rupin-r/MPU6050_MotionTracking_ProofofConcept/imu_fixed_inputs_no_softmax/cnn.c

/*******************************************************************************
* Copyright (C) 2019-2024 Maxim Integrated Products, Inc., All rights Reserved.
*
* This software is protected by copyright laws of the United States and
* of foreign countries. This material may also be protected by patent laws
* and technology transfer regulations of the United States and of foreign
* countries. This software is furnished under a license agreement and/or a
* nondisclosure agreement and may only be used or reproduced in accordance
* with the terms of those agreements. Dissemination of this information to
* any party or parties not specified in the license agreement and/or
* nondisclosure agreement is expressly prohibited.
*
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
* Except as contained in this notice, the name of Maxim Integrated
* Products, Inc. shall not be used except as stated in the Maxim Integrated
* Products, Inc. Branding Policy.
*
* The mere transfer of this software does not imply any licenses
* of trade secrets, proprietary technology, copyrights, patents,
* trademarks, maskwork rights, or any other form of intellectual
* property whatsoever. Maxim Integrated Products, Inc. retains all
* ownership rights.
*******************************************************************************/

// imu_fixed_inputs_no_softmax
// This file was @generated by ai8xize.py --verbose --test-dir demos --prefix imu_fixed_inputs_no_softmax --checkpoint-file trained/imu_q8.pth.tar --config-file networks/imu.yaml --device MAX78000 --compact-data

// DO NOT EDIT - regenerate this file instead!

// Configuring 6 layers
// Input data: HWC
// Layer 0: 30x6x6, no pooling, convtranspose2d with kernel size 3x3, stride 2/2, pad 1/1, no activation, 16x12x12 output
// Layer 1: 16x12x12, no pooling, convtranspose2d with kernel size 3x3, stride 2/2, pad 1/1, no activation, 8x24x24 output
// Layer 2: 8x24x24, no pooling, conv2d with kernel size 3x3, stride 1/1, pad 1/1, ReLU, 8x24x24 output
// Layer 3: 8x24x24, max pool 2x2 with stride 2/2, conv2d with kernel size 3x3, stride 1/1, pad 1/1, ReLU, 8x12x12 output
// Layer 4: 8x12x12, max pool 4x4 with stride 4/4, conv2d with kernel size 3x3, stride 1/1, pad 1/1, ReLU, 5x3x3 output
// Layer 5: 5x3x3 flattened to 45x1x1, no pooling, linear, no activation, 5x1x1 output

// Final Scales: {0: 0, 1: 0, 2: 0, 3: 0, 4: 0, 5: 6}

#include <stdlib.h>
#include <stdint.h>
#include <string.h>
#include <stdio.h>
#include "mxc.h"
#include "gcfr_regs.h"
#include "cnn.h"
#include "weights.h"

void CNN_ISR(void)
{
  // Acknowledge interrupt to all quadrants
  *((volatile uint32_t *) 0x50100000) &= ~((1<<12) | 1);
  *((volatile uint32_t *) 0x50500000) &= ~((1<<12) | 1);
  *((volatile uint32_t *) 0x50900000) &= ~((1<<12) | 1);
  *((volatile uint32_t *) 0x50d00000) &= ~((1<<12) | 1);

  CNN_COMPLETE; // Signal that processing is complete
#ifdef CNN_INFERENCE_TIMER
  cnn_time = MXC_TMR_SW_Stop(CNN_INFERENCE_TIMER);
#else
  cnn_time = 1;
#endif
}

int cnn_continue(void)
{
  cnn_time = 0;

  *((volatile uint32_t *) 0x50100000) |= 1; // Re-enable quadrant 0

  return CNN_OK;
}

int cnn_stop(void)
{
  *((volatile uint32_t *) 0x50100000) &= ~1; // Disable quadrant 0

  return CNN_OK;
}

void memcpy32(uint32_t *dst, const uint32_t *src, int n)
{
  while (n-- > 0) {
    *dst++ = *src++;
  }
}

static const uint32_t kernels[] = KERNELS;

int cnn_load_weights(void)
{
  uint32_t len;
  volatile uint32_t *addr;
  const uint32_t *ptr = kernels;

  while ((addr = (volatile uint32_t *) *ptr++) != 0) {
    *((volatile uint8_t *) ((uint32_t) addr | 1)) = 0x01; // Set address
    len = *ptr++;
    while (len-- > 0)
      *addr++ = *ptr++;
  }

  return CNN_OK;
}

static const uint8_t bias_0[] = BIAS_0;
static const uint8_t bias_1[] = BIAS_1;
static const uint8_t bias_2[] = BIAS_2;
static const uint8_t bias_3[] = BIAS_3;

static void memcpy_8to32(uint32_t *dst, const uint8_t *src, int n)
{
  while (n-- > 0) {
    *dst++ = *src++;
  }
}

int cnn_load_bias(void)
{
  memcpy_8to32((uint32_t *) 0x50108000, bias_0, sizeof(uint8_t) * 13);
  memcpy_8to32((uint32_t *) 0x50508000, bias_1, sizeof(uint8_t) * 16);
  memcpy_8to32((uint32_t *) 0x50908000, bias_2, sizeof(uint8_t) * 13);
  memcpy_8to32((uint32_t *) 0x50d08000, bias_3, sizeof(uint8_t) * 8);

  return CNN_OK;
}

int cnn_init(void)
{
  *((volatile uint32_t *) 0x50001000) = 0x00000000; // AON control
  *((volatile uint32_t *) 0x50100000) = 0x00100008; // Stop SM
  *((volatile uint32_t *) 0x50100004) = 0x0000040e; // SRAM control
  *((volatile uint32_t *) 0x50100008) = 0x00000005; // Layer count
  *((volatile uint32_t *) 0x50500000) = 0x00100008; // Stop SM
  *((volatile uint32_t *) 0x50500004) = 0x0000040e; // SRAM control
  *((volatile uint32_t *) 0x50500008) = 0x00000005; // Layer count
  *((volatile uint32_t *) 0x50900000) = 0x00100008; // Stop SM
  *((volatile uint32_t *) 0x50900004) = 0x0000040e; // SRAM control
  *((volatile uint32_t *) 0x50900008) = 0x00000005; // Layer count
  *((volatile uint32_t *) 0x50d00000) = 0x00100008; // Stop SM
  *((volatile uint32_t *) 0x50d00004) = 0x0000040e; // SRAM control
  *((volatile uint32_t *) 0x50d00008) = 0x00000005; // Layer count

  return CNN_OK;
}

int cnn_configure(void)
{
  // Layer 0 quadrant 0
  *((volatile uint32_t *) 0x50100010) = 0x0001000d; // Rows
  *((volatile uint32_t *) 0x50100090) = 0x0001000d; // Columns
  *((volatile uint32_t *) 0x50100310) = 0x00011000; // SRAM write ptr
  *((volatile uint32_t *) 0x50100410) = 0x00002000; // Write ptr mask offs
  *((volatile uint32_t *) 0x50100590) = 0x00002920; // Layer control
  *((volatile uint32_t *) 0x50100a10) = 0x00007800; // Layer control 2
  *((volatile uint32_t *) 0x50100610) = 0x00000078; // Mask offset and count
  *((volatile uint32_t *) 0x50100690) = 0x0000000b; // TRAM ptr max
  *((volatile uint32_t *) 0x50100790) = 0x10028000; // Post processing register
  *((volatile uint32_t *) 0x50100710) = 0xffffffff; // Mask and processor enables

  // Layer 0 quadrant 1
  *((volatile uint32_t *) 0x50500010) = 0x0001000d; // Rows
  *((volatile uint32_t *) 0x50500090) = 0x0001000d; // Columns
  *((volatile uint32_t *) 0x50500310) = 0x00011000; // SRAM write ptr
  *((volatile uint32_t *) 0x50500410) = 0x00002000; // Write ptr mask offs
  *((volatile uint32_t *) 0x50500590) = 0x00000920; // Layer control
  *((volatile uint32_t *) 0x50500a10) = 0x00007800; // Layer control 2
  *((volatile uint32_t *) 0x50500610) = 0x00000078; // Mask offset and count
  *((volatile uint32_t *) 0x50500690) = 0x0000000b; // TRAM ptr max
  *((volatile uint32_t *) 0x50500790) = 0x10029000; // Post processing register
  *((volatile uint32_t *) 0x50500710) = 0x3fff3fff; // Mask and processor enables

  // Layer 0 quadrant 2
  *((volatile uint32_t *) 0x50900010) = 0x0001000d; // Rows
  *((volatile uint32_t *) 0x50900090) = 0x0001000d; // Columns
  *((volatile uint32_t *) 0x50900310) = 0x00011000; // SRAM write ptr
  *((volatile uint32_t *) 0x50900410) = 0x00002000; // Write ptr mask offs
  *((volatile uint32_t *) 0x50900590) = 0x00000920; // Layer control
  *((volatile uint32_t *) 0x50900a10) = 0x00007800; // Layer control 2
  *((volatile uint32_t *) 0x50900610) = 0x00000078; // Mask offset and count
  *((volatile uint32_t *) 0x50900690) = 0x0000000b; // TRAM ptr max
  *((volatile uint32_t *) 0x50900790) = 0x10028000; // Post processing register

  // Layer 0 quadrant 3
  *((volatile uint32_t *) 0x50d00010) = 0x0001000d; // Rows
  *((volatile uint32_t *) 0x50d00090) = 0x0001000d; // Columns
  *((volatile uint32_t *) 0x50d00310) = 0x00011000; // SRAM write ptr
  *((volatile uint32_t *) 0x50d00410) = 0x00002000; // Write ptr mask offs
  *((volatile uint32_t *) 0x50d00590) = 0x00000920; // Layer control
  *((volatile uint32_t *) 0x50d00a10) = 0x00007800; // Layer control 2
  *((volatile uint32_t *) 0x50d00610) = 0x00000078; // Mask offset and count
  *((volatile uint32_t *) 0x50d00690) = 0x0000000b; // TRAM ptr max
  *((volatile uint32_t *) 0x50d00790) = 0x10028000; // Post processing register

  // Layer 1 quadrant 0
  *((volatile uint32_t *) 0x50100014) = 0x00010019; // Rows
  *((volatile uint32_t *) 0x50100094) = 0x00010019; // Columns
  *((volatile uint32_t *) 0x50100314) = 0x0001c000; // SRAM write ptr
  *((volatile uint32_t *) 0x50100414) = 0x00002000; // Write ptr mask offs
  *((volatile uint32_t *) 0x50100514) = 0x00001000; // SRAM read ptr
  *((volatile uint32_t *) 0x50100594) = 0x00004920; // Layer control
  *((volatile uint32_t *) 0x50100a14) = 0x00003800; // Layer control 2
  *((volatile uint32_t *) 0x50100614) = 0x00000038; // Mask offset and count
  *((volatile uint32_t *) 0x50100694) = 0x00000017; // TRAM ptr max
  *((volatile uint32_t *) 0x50100794) = 0x10022000; // Post processing register

  // Layer 1 quadrant 1
  *((volatile uint32_t *) 0x50500014) = 0x00010019; // Rows
  *((volatile uint32_t *) 0x50500094) = 0x00010019; // Columns
  *((volatile uint32_t *) 0x50500314) = 0x0001c000; // SRAM write ptr
  *((volatile uint32_t *) 0x50500414) = 0x00002000; // Write ptr mask offs
  *((volatile uint32_t *) 0x50500514) = 0x00001000; // SRAM read ptr
  *((volatile uint32_t *) 0x50500594) = 0x00000920; // Layer control
  *((volatile uint32_t *) 0x50500a14) = 0x00003800; // Layer control 2
  *((volatile uint32_t *) 0x50500614) = 0x00000038; // Mask offset and count
  *((volatile uint32_t *) 0x50500694) = 0x00000017; // TRAM ptr max
  *((volatile uint32_t *) 0x50500794) = 0x10022000; // Post processing register

  // Layer 1 quadrant 2
  *((volatile uint32_t *) 0x50900014) = 0x00010019; // Rows
  *((volatile uint32_t *) 0x50900094) = 0x00010019; // Columns
  *((volatile uint32_t *) 0x50900314) = 0x0001c000; // SRAM write ptr
  *((volatile uint32_t *) 0x50900414) = 0x00002000; // Write ptr mask offs
  *((volatile uint32_t *) 0x50900514) = 0x00001000; // SRAM read ptr
  *((volatile uint32_t *) 0x50900594) = 0x00000920; // Layer control
  *((volatile uint32_t *) 0x50900a14) = 0x00003800; // Layer control 2
  *((volatile uint32_t *) 0x50900614) = 0x00000038; // Mask offset and count
  *((volatile uint32_t *) 0x50900694) = 0x00000017; // TRAM ptr max
  *((volatile uint32_t *) 0x50900794) = 0x10023000; // Post processing register
  *((volatile uint32_t *) 0x50900714) = 0xffffffff; // Mask and processor enables

  // Layer 1 quadrant 3
  *((volatile uint32_t *) 0x50d00014) = 0x00010019; // Rows
  *((volatile uint32_t *) 0x50d00094) = 0x00010019; // Columns
  *((volatile uint32_t *) 0x50d00314) = 0x0001c000; // SRAM write ptr
  *((volatile uint32_t *) 0x50d00414) = 0x00002000; // Write ptr mask offs
  *((volatile uint32_t *) 0x50d00514) = 0x00001000; // SRAM read ptr
  *((volatile uint32_t *) 0x50d00594) = 0x00000920; // Layer control
  *((volatile uint32_t *) 0x50d00a14) = 0x00003800; // Layer control 2
  *((volatile uint32_t *) 0x50d00614) = 0x00000038; // Mask offset and count
  *((volatile uint32_t *) 0x50d00694) = 0x00000017; // TRAM ptr max
  *((volatile uint32_t *) 0x50d00794) = 0x10022000; // Post processing register

  // Layer 2 quadrant 0
  *((volatile uint32_t *) 0x50100018) = 0x00010019; // Rows
  *((volatile uint32_t *) 0x50100098) = 0x00010019; // Columns
  *((volatile uint32_t *) 0x50100318) = 0x00019000; // SRAM write ptr
  *((volatile uint32_t *) 0x50100418) = 0x00002000; // Write ptr mask offs
  *((volatile uint32_t *) 0x50100598) = 0x00008b20; // Layer control
  *((volatile uint32_t *) 0x50100a18) = 0x00003800; // Layer control 2
  *((volatile uint32_t *) 0x50100618) = 0x00000038; // Mask offset and count
  *((volatile uint32_t *) 0x50100698) = 0x00000017; // TRAM ptr max
  *((volatile uint32_t *) 0x50100798) = 0x00022000; // Post processing register

  // Layer 2 quadrant 1
  *((volatile uint32_t *) 0x50500018) = 0x00010019; // Rows
  *((volatile uint32_t *) 0x50500098) = 0x00010019; // Columns
  *((volatile uint32_t *) 0x50500318) = 0x00019000; // SRAM write ptr
  *((volatile uint32_t *) 0x50500418) = 0x00002000; // Write ptr mask offs
  *((volatile uint32_t *) 0x50500598) = 0x00000b20; // Layer control
  *((volatile uint32_t *) 0x50500a18) = 0x00003800; // Layer control 2
  *((volatile uint32_t *) 0x50500618) = 0x00000038; // Mask offset and count
  *((volatile uint32_t *) 0x50500698) = 0x00000017; // TRAM ptr max
  *((volatile uint32_t *) 0x50500798) = 0x00022000; // Post processing register

  // Layer 2 quadrant 2
  *((volatile uint32_t *) 0x50900018) = 0x00010019; // Rows
  *((volatile uint32_t *) 0x50900098) = 0x00010019; // Columns
  *((volatile uint32_t *) 0x50900318) = 0x00019000; // SRAM write ptr
  *((volatile uint32_t *) 0x50900418) = 0x00002000; // Write ptr mask offs
  *((volatile uint32_t *) 0x50900598) = 0x00000b20; // Layer control
  *((volatile uint32_t *) 0x50900a18) = 0x00003800; // Layer control 2
  *((volatile uint32_t *) 0x50900618) = 0x00000038; // Mask offset and count
  *((volatile uint32_t *) 0x50900698) = 0x00000017; // TRAM ptr max
  *((volatile uint32_t *) 0x50900798) = 0x00022000; // Post processing register

  // Layer 2 quadrant 3
  *((volatile uint32_t *) 0x50d00018) = 0x00010019; // Rows
  *((volatile uint32_t *) 0x50d00098) = 0x00010019; // Columns
  *((volatile uint32_t *) 0x50d00318) = 0x00019000; // SRAM write ptr
  *((volatile uint32_t *) 0x50d00418) = 0x00002000; // Write ptr mask offs
  *((volatile uint32_t *) 0x50d00598) = 0x00000b20; // Layer control
  *((volatile uint32_t *) 0x50d00a18) = 0x00003800; // Layer control 2
  *((volatile uint32_t *) 0x50d00618) = 0x00000038; // Mask offset and count
  *((volatile uint32_t *) 0x50d00698) = 0x00000017; // TRAM ptr max
  *((volatile uint32_t *) 0x50d00798) = 0x00023000; // Post processing register
  *((volatile uint32_t *) 0x50d00718) = 0xff00ff00; // Mask and processor enables

  // Layer 3 quadrant 0
  *((volatile uint32_t *) 0x5010001c) = 0x00010019; // Rows
  *((volatile uint32_t *) 0x5010009c) = 0x00010019; // Columns
  *((volatile uint32_t *) 0x5010019c) = 0x00000001; // Pooling rows
  *((volatile uint32_t *) 0x5010021c) = 0x00000001; // Pooling columns
  *((volatile uint32_t *) 0x5010029c) = 0x00000001; // Stride
  *((volatile uint32_t *) 0x5010041c) = 0x00002000; // Write ptr mask offs
  *((volatile uint32_t *) 0x5010051c) = 0x00001000; // SRAM read ptr
  *((volatile uint32_t *) 0x5010059c) = 0x00008ba0; // Layer control
  *((volatile uint32_t *) 0x50100a1c) = 0x00003800; // Layer control 2
  *((volatile uint32_t *) 0x5010061c) = 0x00000038; // Mask offset and count
  *((volatile uint32_t *) 0x5010069c) = 0x0000000b; // TRAM ptr max
  *((volatile uint32_t *) 0x5010079c) = 0x00023005; // Post processing register

  // Layer 3 quadrant 1
  *((volatile uint32_t *) 0x5050001c) = 0x00010019; // Rows
  *((volatile uint32_t *) 0x5050009c) = 0x00010019; // Columns
  *((volatile uint32_t *) 0x5050019c) = 0x00000001; // Pooling rows
  *((volatile uint32_t *) 0x5050021c) = 0x00000001; // Pooling columns
  *((volatile uint32_t *) 0x5050029c) = 0x00000001; // Stride
  *((volatile uint32_t *) 0x5050041c) = 0x00002000; // Write ptr mask offs
  *((volatile uint32_t *) 0x5050051c) = 0x00001000; // SRAM read ptr
  *((volatile uint32_t *) 0x5050059c) = 0x00000ba0; // Layer control
  *((volatile uint32_t *) 0x50500a1c) = 0x00003800; // Layer control 2
  *((volatile uint32_t *) 0x5050061c) = 0x00000038; // Mask offset and count
  *((volatile uint32_t *) 0x5050069c) = 0x0000000b; // TRAM ptr max
  *((volatile uint32_t *) 0x5050079c) = 0x00022000; // Post processing register

  // Layer 3 quadrant 2
  *((volatile uint32_t *) 0x5090001c) = 0x00010019; // Rows
  *((volatile uint32_t *) 0x5090009c) = 0x00010019; // Columns
  *((volatile uint32_t *) 0x5090019c) = 0x00000001; // Pooling rows
  *((volatile uint32_t *) 0x5090021c) = 0x00000001; // Pooling columns
  *((volatile uint32_t *) 0x5090029c) = 0x00000001; // Stride
  *((volatile uint32_t *) 0x5090041c) = 0x00002000; // Write ptr mask offs
  *((volatile uint32_t *) 0x5090051c) = 0x00001000; // SRAM read ptr
  *((volatile uint32_t *) 0x5090059c) = 0x00000ba0; // Layer control
  *((volatile uint32_t *) 0x50900a1c) = 0x00003800; // Layer control 2
  *((volatile uint32_t *) 0x5090061c) = 0x00000038; // Mask offset and count
  *((volatile uint32_t *) 0x5090069c) = 0x0000000b; // TRAM ptr max
  *((volatile uint32_t *) 0x5090079c) = 0x00022000; // Post processing register

  // Layer 3 quadrant 3
  *((volatile uint32_t *) 0x50d0001c) = 0x00010019; // Rows
  *((volatile uint32_t *) 0x50d0009c) = 0x00010019; // Columns
  *((volatile uint32_t *) 0x50d0019c) = 0x00000001; // Pooling rows
  *((volatile uint32_t *) 0x50d0021c) = 0x00000001; // Pooling columns
  *((volatile uint32_t *) 0x50d0029c) = 0x00000001; // Stride
  *((volatile uint32_t *) 0x50d0041c) = 0x00002000; // Write ptr mask offs
  *((volatile uint32_t *) 0x50d0051c) = 0x00001000; // SRAM read ptr
  *((volatile uint32_t *) 0x50d0059c) = 0x00000ba0; // Layer control
  *((volatile uint32_t *) 0x50d00a1c) = 0x00003800; // Layer control 2
  *((volatile uint32_t *) 0x50d0061c) = 0x00000038; // Mask offset and count
  *((volatile uint32_t *) 0x50d0069c) = 0x0000000b; // TRAM ptr max
  *((volatile uint32_t *) 0x50d0079c) = 0x00022000; // Post processing register
  *((volatile uint32_t *) 0x50d0071c) = 0x00ff00ff; // Mask and processor enables

  // Layer 4 quadrant 0
  *((volatile uint32_t *) 0x50100020) = 0x0001000d; // Rows
  *((volatile uint32_t *) 0x501000a0) = 0x0001000d; // Columns
  *((volatile uint32_t *) 0x501001a0) = 0x00000003; // Pooling rows
  *((volatile uint32_t *) 0x50100220) = 0x00000003; // Pooling columns
  *((volatile uint32_t *) 0x501002a0) = 0x00000003; // Stride
  *((volatile uint32_t *) 0x50100320) = 0x00005000; // SRAM write ptr
  *((volatile uint32_t *) 0x50100420) = 0x00002000; // Write ptr mask offs
  *((volatile uint32_t *) 0x501005a0) = 0x00004ba0; // Layer control
  *((volatile uint32_t *) 0x50100a20) = 0x00002000; // Layer control 2
  *((volatile uint32_t *) 0x50100620) = 0x008000a0; // Mask offset and count
  *((volatile uint32_t *) 0x501006a0) = 0x00000002; // TRAM ptr max
  *((volatile uint32_t *) 0x501007a0) = 0x00002000; // Post processing register
  *((volatile uint32_t *) 0x50100720) = 0x00ff00ff; // Mask and processor enables

  // Layer 4 quadrant 1
  *((volatile uint32_t *) 0x50500020) = 0x0001000d; // Rows
  *((volatile uint32_t *) 0x505000a0) = 0x0001000d; // Columns
  *((volatile uint32_t *) 0x505001a0) = 0x00000003; // Pooling rows
  *((volatile uint32_t *) 0x50500220) = 0x00000003; // Pooling columns
  *((volatile uint32_t *) 0x505002a0) = 0x00000003; // Stride
  *((volatile uint32_t *) 0x50500320) = 0x00005000; // SRAM write ptr
  *((volatile uint32_t *) 0x50500420) = 0x00002000; // Write ptr mask offs
  *((volatile uint32_t *) 0x505005a0) = 0x00000ba0; // Layer control
  *((volatile uint32_t *) 0x50500a20) = 0x00002000; // Layer control 2
  *((volatile uint32_t *) 0x50500620) = 0x008000a0; // Mask offset and count
  *((volatile uint32_t *) 0x505006a0) = 0x00000002; // TRAM ptr max
  *((volatile uint32_t *) 0x505007a0) = 0x00002000; // Post processing register

  // Layer 4 quadrant 2
  *((volatile uint32_t *) 0x50900020) = 0x0001000d; // Rows
  *((volatile uint32_t *) 0x509000a0) = 0x0001000d; // Columns
  *((volatile uint32_t *) 0x509001a0) = 0x00000003; // Pooling rows
  *((volatile uint32_t *) 0x50900220) = 0x00000003; // Pooling columns
  *((volatile uint32_t *) 0x509002a0) = 0x00000003; // Stride
  *((volatile uint32_t *) 0x50900320) = 0x00005000; // SRAM write ptr
  *((volatile uint32_t *) 0x50900420) = 0x00002000; // Write ptr mask offs
  *((volatile uint32_t *) 0x509005a0) = 0x00000ba0; // Layer control
  *((volatile uint32_t *) 0x50900a20) = 0x00002000; // Layer control 2
  *((volatile uint32_t *) 0x50900620) = 0x008000a0; // Mask offset and count
  *((volatile uint32_t *) 0x509006a0) = 0x00000002; // TRAM ptr max
  *((volatile uint32_t *) 0x509007a0) = 0x00003008; // Post processing register

  // Layer 4 quadrant 3
  *((volatile uint32_t *) 0x50d00020) = 0x0001000d; // Rows
  *((volatile uint32_t *) 0x50d000a0) = 0x0001000d; // Columns
  *((volatile uint32_t *) 0x50d001a0) = 0x00000003; // Pooling rows
  *((volatile uint32_t *) 0x50d00220) = 0x00000003; // Pooling columns
  *((volatile uint32_t *) 0x50d002a0) = 0x00000003; // Stride
  *((volatile uint32_t *) 0x50d00320) = 0x00005000; // SRAM write ptr
  *((volatile uint32_t *) 0x50d00420) = 0x00002000; // Write ptr mask offs
  *((volatile uint32_t *) 0x50d005a0) = 0x00000ba0; // Layer control
  *((volatile uint32_t *) 0x50d00a20) = 0x00002000; // Layer control 2
  *((volatile uint32_t *) 0x50d00620) = 0x008000a0; // Mask offset and count
  *((volatile uint32_t *) 0x50d006a0) = 0x00000002; // TRAM ptr max
  *((volatile uint32_t *) 0x50d007a0) = 0x00002000; // Post processing register

  // Layer 5 quadrant 0
  *((volatile uint32_t *) 0x501003a4) = 0x00000001; // Write ptr time slot offs
  *((volatile uint32_t *) 0x50100424) = 0x00002000; // Write ptr mask offs
  *((volatile uint32_t *) 0x50100524) = 0x00001000; // SRAM read ptr
  *((volatile uint32_t *) 0x501005a4) = 0x00000920; // Layer control
  *((volatile uint32_t *) 0x50100a24) = 0x00002008; // Layer control 2
  *((volatile uint32_t *) 0x50100624) = 0x048005e0; // Mask offset and count
  *((volatile uint32_t *) 0x50100124) = 0x00000100; // 1D
  *((volatile uint32_t *) 0x501007a4) = 0x00003000; // Post processing register
  *((volatile uint32_t *) 0x50100724) = 0x1f001f00; // Mask and processor enables

  // Layer 5 quadrant 1
  *((volatile uint32_t *) 0x505003a4) = 0x00000001; // Write ptr time slot offs
  *((volatile uint32_t *) 0x50500424) = 0x00002000; // Write ptr mask offs
  *((volatile uint32_t *) 0x50500524) = 0x00001000; // SRAM read ptr
  *((volatile uint32_t *) 0x505005a4) = 0x00000920; // Layer control
  *((volatile uint32_t *) 0x50500a24) = 0x00002008; // Layer control 2
  *((volatile uint32_t *) 0x50500624) = 0x048005e0; // Mask offset and count
  *((volatile uint32_t *) 0x50500124) = 0x00000100; // 1D
  *((volatile uint32_t *) 0x505007a4) = 0x00002000; // Post processing register

  // Layer 5 quadrant 2
  *((volatile uint32_t *) 0x509003a4) = 0x00000001; // Write ptr time slot offs
  *((volatile uint32_t *) 0x50900424) = 0x00002000; // Write ptr mask offs
  *((volatile uint32_t *) 0x50900524) = 0x00001000; // SRAM read ptr
  *((volatile uint32_t *) 0x509005a4) = 0x00000920; // Layer control
  *((volatile uint32_t *) 0x50900a24) = 0x00002008; // Layer control 2
  *((volatile uint32_t *) 0x50900624) = 0x048005e0; // Mask offset and count
  *((volatile uint32_t *) 0x50900124) = 0x00000100; // 1D
  *((volatile uint32_t *) 0x509007a4) = 0x00002000; // Post processing register

  // Layer 5 quadrant 3
  *((volatile uint32_t *) 0x50d003a4) = 0x00000001; // Write ptr time slot offs
  *((volatile uint32_t *) 0x50d00424) = 0x00002000; // Write ptr mask offs
  *((volatile uint32_t *) 0x50d00524) = 0x00001000; // SRAM read ptr
  *((volatile uint32_t *) 0x50d005a4) = 0x00000920; // Layer control
  *((volatile uint32_t *) 0x50d00a24) = 0x00002008; // Layer control 2
  *((volatile uint32_t *) 0x50d00624) = 0x048005e0; // Mask offset and count
  *((volatile uint32_t *) 0x50d00124) = 0x00000100; // 1D
  *((volatile uint32_t *) 0x50d007a4) = 0x00002000; // Post processing register


  return CNN_OK;
}

int cnn_start(void)
{
  cnn_time = 0;

  *((volatile uint32_t *) 0x50100000) = 0x00100808; // Enable quadrant 0
  *((volatile uint32_t *) 0x50500000) = 0x00100809; // Enable quadrant 1
  *((volatile uint32_t *) 0x50900000) = 0x00100809; // Enable quadrant 2
  *((volatile uint32_t *) 0x50d00000) = 0x00100809; // Enable quadrant 3

#ifdef CNN_INFERENCE_TIMER
  MXC_TMR_SW_Start(CNN_INFERENCE_TIMER);
#endif

  CNN_START; // Allow capture of processing time
  *((volatile uint32_t *) 0x50100000) = 0x00100009; // Master enable quadrant 0

  return CNN_OK;
}

int cnn_unload(uint32_t *out_buf32)
{
  uint16_t *out_buf = (uint16_t *) out_buf32;
  uint32_t val;
  volatile uint32_t *addr;
  int i;

  // Custom unload for this network, layer 5 (fc_Gemm_4): 8-bit data, shape: (5, 1, 1)
  addr = (volatile uint32_t *) 0x50400000;
  for (i = 0; i < 2; i++) {
    val = *addr;
    addr +=  0x2000;
    *out_buf++ = (int16_t)((val & 0xff)) << 6;
    *out_buf++ = (int16_t)(((val >> 8) & 0xff)) << 6;
    *out_buf++ = (int16_t)(((val >> 16) & 0xff)) << 6;
    *out_buf++ = (int16_t)(((val >> 24) & 0xff)) << 6;
  }

  return CNN_OK;
}

int cnn_enable(uint32_t clock_source, uint32_t clock_divider)
{
  // Reset all domains, restore power to CNN
  MXC_GCFR->reg3 = 0xf; // Reset
  MXC_GCFR->reg1 = 0xf; // Mask memory
  MXC_GCFR->reg0 = 0xf; // Power
  MXC_GCFR->reg2 = 0x0; // Iso
  MXC_GCFR->reg3 = 0x0; // Reset

  MXC_GCR->pclkdiv = (MXC_GCR->pclkdiv & ~(MXC_F_GCR_PCLKDIV_CNNCLKDIV | MXC_F_GCR_PCLKDIV_CNNCLKSEL))
                     | clock_divider | clock_source;
  MXC_SYS_ClockEnable(MXC_SYS_PERIPH_CLOCK_CNN); // Enable CNN clock

  MXC_NVIC_SetVector(CNN_IRQn, CNN_ISR); // Set CNN complete vector

  return CNN_OK;
}

int cnn_boost_enable(mxc_gpio_regs_t *port, uint32_t pin)
{
  mxc_gpio_cfg_t gpio_out;
  gpio_out.port = port;
  gpio_out.mask = pin;
  gpio_out.pad = MXC_GPIO_PAD_NONE;
  gpio_out.func = MXC_GPIO_FUNC_OUT;
  MXC_GPIO_Config(&gpio_out);
  MXC_GPIO_OutSet(gpio_out.port, gpio_out.mask);

  return CNN_OK;
}

int cnn_boost_disable(mxc_gpio_regs_t *port, uint32_t pin)
{
  mxc_gpio_cfg_t gpio_out;
  gpio_out.port = port;
  gpio_out.mask = pin;
  gpio_out.pad = MXC_GPIO_PAD_NONE;
  gpio_out.func = MXC_GPIO_FUNC_OUT;
  MXC_GPIO_Config(&gpio_out);
  MXC_GPIO_OutClr(gpio_out.port, gpio_out.mask);

  return CNN_OK;
}

int cnn_disable(void)
{
  // Disable CNN clock
  MXC_SYS_ClockDisable(MXC_SYS_PERIPH_CLOCK_CNN);

  // Disable power to CNN
  MXC_GCFR->reg3 = 0xf; // Reset
  MXC_GCFR->reg2 |= 0xf; // Iso
  MXC_GCFR->reg0 = 0x0; // Power
  MXC_GCFR->reg1 = 0x0; // Mask memory
  MXC_GCFR->reg3 = 0x0; // Reset

  return CNN_OK;
}
