rupin-r/MPU6050_MotionTracking_ProofofConcept/imu_fixed_inputs_no_softmax/weights.h

// This file was @generated automatically

#define BIAS_0 { \
  0xfe, 0x01, 0xfe, 0x03, 0xff, 0x00, 0xff, 0x00, 0xff, 0x00, 0x00, 0x00, 0xff \
}
#define BIAS_1 { \
  0x00, 0x00, 0x00, 0xff, 0x00, 0x00, 0x00, 0xff, 0x00, 0xff, 0x00, 0x00, 0xff, 0xff, 0x00, 0x00 \
}
#define BIAS_2 { \
  0x00, 0x00, 0xff, 0xff, 0x00, 0xff, 0xff, 0x00, 0xff, 0x00, 0xff, 0x00, 0x00 \
}
#define BIAS_3 { \
  0x00, 0xff, 0xff, 0x00, 0xff, 0x00, 0xff, 0x00 \
}
#define KERNELS { \
  0x50180000, 0x00000030, 0x1f2f0c03, 0xf5d113e1, 0xdb1bff0d, 0x01030af6, 0x15de2fe5, 0x1b0cf109, \
  0xf60ae3c3, 0xf3f6ea28, 0x13f52450, 0x22da16db, 0xf8111221, 0xe728d930, 0xe8f8f0e1, 0x2ef6dc0f, \
  0xd40dd3e9, 0x14d60be7, 0xe310f3eb, 0x3d051dfe, 0xed09f90f, 0x07dffee8, 0x1dccead6, 0xfaff27fc, \
  0x4731fbdf, 0xfe08e237, 0xeb1de8ed, 0x1ede08f5, 0x0d01e318, 0xe805e903, 0x210afaed, 0x33fe16d9, \
  0x10e3e11a, 0xf1fed1ff, 0xd9d5f22e, 0x0ef62ee3, 0xfde2fce8, 0xcef70d21, 0x030602f7, 0xf90816f8, \
  0x0d030f03, 0x1919fff9, 0x00fc0a10, 0x06fe06fd, 0xf108efef, 0xfff9070d, 0x0b0c1dfb, 0x0cf40af6, \
  0x05f60003, 0x13000000, 0x50184000, 0x00000030, 0x222a0320, 0xccf4f4bd, 0xc10af40f, 0xe70ff8ff, \
  0x38d333d4, 0x2debfaf4, 0xe815f0cb, 0xcfd4fd25, 0xfb042045, 0x21dd19ed, 0xf60eed3c, 0xf91af20a, \
  0xd6fde1f6, 0x4103ec2f, 0xf70bd901, 0x19d70b02, 0xe809f607, 0x2be13609, 0xfff8d7f6, 0x16e1120a, \
  0x15defde4, 0xfc090f01, 0x4b1c02d5, 0x1206f002, 0xda2adaf1, 0x1dfb0fd5, 0xfd07e826, 0xd9fbe615, \
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
  0xef26fa01, 0x031beae2, 0x37db23e4, 0x0ee8050a, 0xf018dac5, 0xeee9d719, 0x09f71319, 0x28d008e7, \
  0xfd21ef31, 0xde27ee34, 0xe70603f0, 0x16f3f836, 0xd906ebf5, 0x12f11c14, 0xe908ee03, 0x0fe2080d, \
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
}
