rupin-r/MPU6050_MotionTracking_ProofofConcept/imu_fixed_inputs_no_softmax/sampledata.h

// This file was @generated automatically

#define SAMPLE_INPUT_0 { \
  0x94838480, 0x83828482, 0x839e9684, 0x84858684, 0x88888f82, 0x858d8382, 0x8f8dce9a, 0x8e99a596, \
  0x999089ee, 0xb0a5f6a8, 0x8382b0f2, 0xa18cb28a, 0x9f93a091, 0x9883aabc, 0x89aebb8e, 0x93829f98, \
  0x82a1ad87, 0x8281829f, 0x9e8dd0c6, 0x86958891, 0x82898c86, 0xa99b8eb1, 0x8c828890, 0x88858792, \
  0xc8a1b8d4, 0x8b839888, 0x8b938790, 0xb1a2cc8e, 0x96849682, 0x918a8396, 0xd995a5a9, 0x89848b97, \
  0x838ca39a, 0x9b878398, 0x8a938381, 0x88878683 \
}
#define SAMPLE_INPUT_4 { \
  0x809b8c9c, 0x83858682, 0x83888589, 0x888b8582, 0x83828598, 0x84848982, 0xb9c990c6, 0xbaa5aeb7, \
  0x998c24e4, 0xacbdb18f, 0xa29c89ea, 0x899da08d, 0x898aa8c2, 0xb68ac3a1, 0x9d88adb5, 0x96928d8e, \
  0x8196a7a2, 0x94848195, 0xc4909b90, 0x9087aa8a, 0x85968497, 0x828d9fa0, 0xa886aa85, 0x80869d9a, \
  0xce8195be, 0x8383948e, 0x8e85a0b0, 0x8882a4ae, 0x8b859192, 0x84828c81, 0xcb95a5bb, 0x8a888f9e, \
  0x8188938d, 0x8e948288, 0x83828280, 0x87868985 \
}
#define SAMPLE_INPUT_8 { \
  0x88918886, 0x82808287, 0x82878c8d, 0x82818183, 0x8c858c84, 0x82838580, 0xa889a4f5, 0xae9cabd0, \
  0xb786acc7, 0x978391b0, 0x948c84fb, 0x89868baa, 0x84848682, 0xc4829d91, 0xa19689a6, 0xb6958790, \
  0x8e9199ac, 0x9193868f, 0xc28686bb, 0x9c888f81, 0x8882acaa, 0x87a294bd, 0x81908594, 0x9e818482, \
  0xb99485be, 0x87808a8f, 0x8a8b8485, 0xc58b8eb3, 0xbd818892, 0x81889a85, 0x84a79dbf, 0x9d8f8694, \
  0x968a9181, 0xa7898281, 0x89808695, 0x8d818183 \
}
#define SAMPLE_INPUT_12 { \
  0x85828b83, 0x80808f8f, 0x84828186, 0x81848782, 0x8381818b, 0x82808484, 0xfceca6a8, 0x8885cfdc, \
  0xa485f785, 0x8f8d979c, 0x03a7a0f4, 0xa6878eaa, 0x868cad93, 0xbd8884be, 0x92818b92, 0x848e9d81, \
  0x9787a993, 0xa78b8883, 0xb09b9e9e, 0x868997c2, 0x89868795, 0x9182cdb9, 0xc29684b4, 0x81878e9b, \
  0xa0aea5bf, 0x8a878796, 0x80878784, 0x86858e92, 0x829e8697, 0x92988d92, 0xa3bd929c, 0xab8a8989, \
  0x938888a0, 0x95868b91, 0x888e9086, 0x9298828e \
}
#define SAMPLE_INPUT_16 { \
  0x86898781, 0x8187918a, 0x88809187, 0x83828688, 0x9186898c, 0x82818382, 0xc1959692, 0x9b8889a3, \
  0x82a292a3, 0xa09a9bbe, 0x9389918e, 0x90978b8f, 0x979e818f, 0xcb8f8ab0, 0xad83839c, 0x81989c8a, \
  0x91908ba5, 0x8d838e8a, 0xd8a090c7, 0x8a898e87, 0x8d928383, 0x9d80988d, 0x839f8183, 0x96848384, \
  0x99b188b8, 0x8687858d, 0x99859283, 0xb98e8f8d, 0xc2a594a6, 0x8e9698ac, 0xccca8c9d, 0xa583848a, \
  0xae988781, 0x9786898a, 0x8d84848a, 0x8585828d \
}
#define SAMPLE_INPUT_20 { \
  0x85819da0, 0x83828486, 0x8d828789, 0x84868b87, 0x8d848280, 0x8283848a, 0x07c9eaa2, 0xd8c3c7a5, \
  0xe48da4aa, 0xa5a89caa, 0xf7c9aae8, 0xa39594ba, 0x9b898490, 0x85b692dd, 0x9d888ea9, 0x8689968b, \
  0xa99483a0, 0x9791818a, 0xbdc284f0, 0x838f82a1, 0x83908982, 0xca83c000, 0x918a839e, 0x8883908d, \
  0xa3ba89dd, 0x99918186, 0x898e8483, 0xc2828292, 0x9e8aa0b8, 0x8a87948c, 0xc3c29486, 0xa2828088, \
  0x87818c84, 0x829d8087, 0x868b8e89, 0x83838c80 \
}
#define SAMPLE_INPUT_24 { \
  0x84878d84, 0x88828581, 0x82808890, 0x85818484, 0x878f8483, 0x82858386, 0x91a88abb, 0xe69a89bb, \
  0x9e9994a1, 0x8288a7af, 0xe2998c89, 0x9c81969e, 0x8b858e82, 0x90b591b0, 0xa1b18c93, 0x8da18782, \
  0x9b9d8795, 0x818f8d84, 0xabc18c8f, 0x92818695, 0x8c8a829a, 0xc68185ac, 0x978a8891, 0x818c8a8a, \
  0xb8b7a093, 0x8a828586, 0x97869189, 0x94b081a6, 0x93c89f89, 0x82969b92, 0xb493af93, 0x8eaf8885, \
  0x8b8d8682, 0x92988284, 0x8f8e8683, 0x84818b8a \
}
#define SAMPLE_INPUT_28 { \
  0x00009da2, 0x00008384, 0x00008780, 0x00008581, 0x00008181, 0x0000868b, 0x0000dca0, 0x000094d7, \
  0x000091c1, 0x00009a87, 0x0000899f, 0x00009094, 0x00008a98, 0x00008dad, 0x0000808a, 0x0000818b, \
  0x000083a6, 0x0000848d, 0x0000a496, 0x0000928f, 0x00008985, 0x00008ea0, 0x0000aa98, 0x0000808e, \
  0x0000a9a7, 0x00008387, 0x00008184, 0x00009092, 0x00009791, 0x00008b87, 0x0000b88b, 0x00008682, \
  0x00008a81, 0x00009194, 0x00008b84, 0x0000828e \
}
